Stormpegy/LeonardoSDVX-Shield/imgs/img-1.png

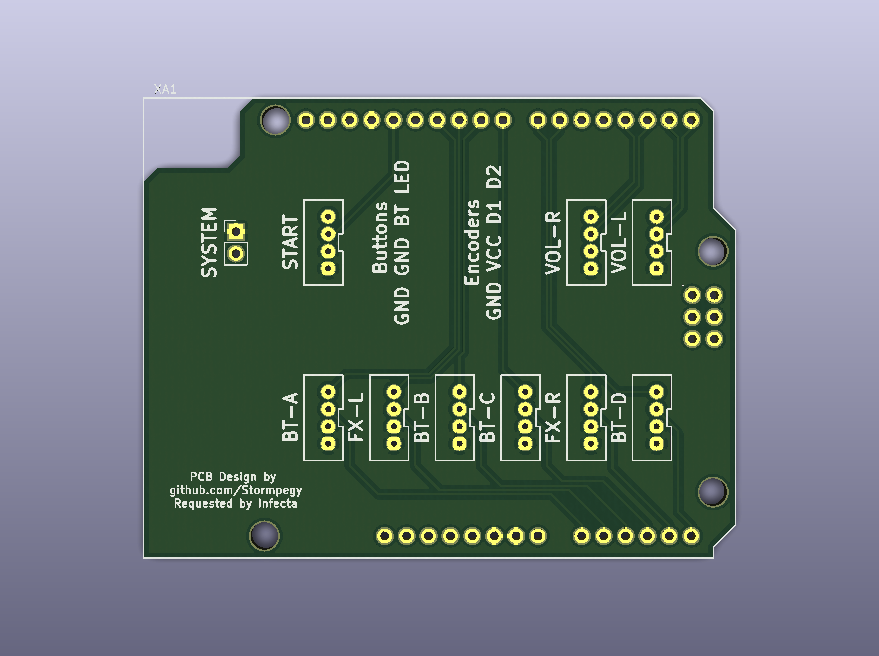
imgs/img-1.png
