Stormpegy/LeonardoSDVX-Shield/imgs/img-2.png

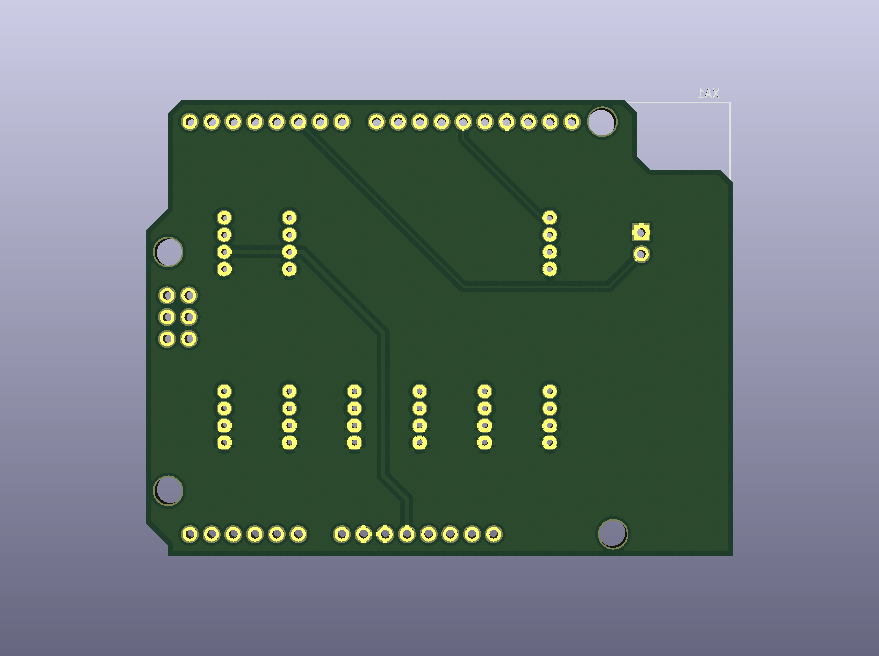
imgs/img-2.png
